sushan6/the-dev-board/assets/back-3d-pcb.PNG

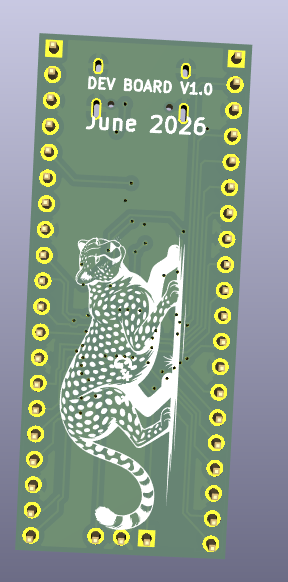
assets/back-3d-pcb.PNG
