sushan6/the-dev-board/assets/cart-1.PNG

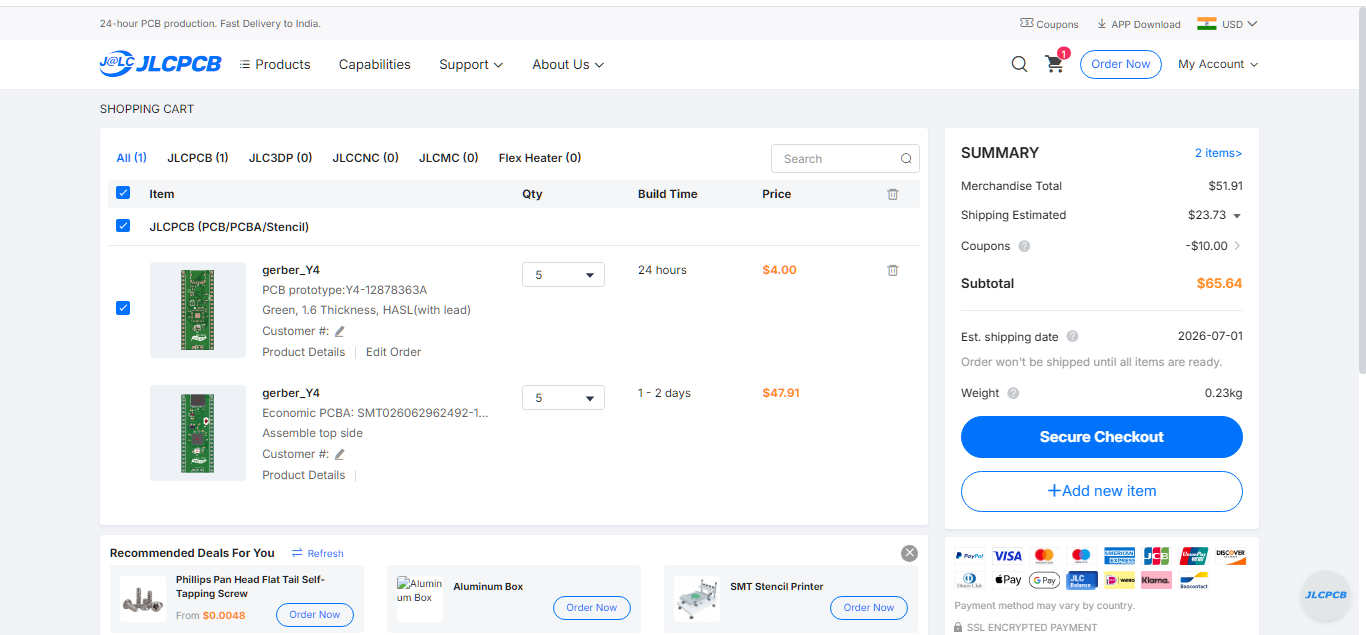
assets/cart-1.PNG
