sushan6/the-dev-board/assets/cart-2-1.PNG

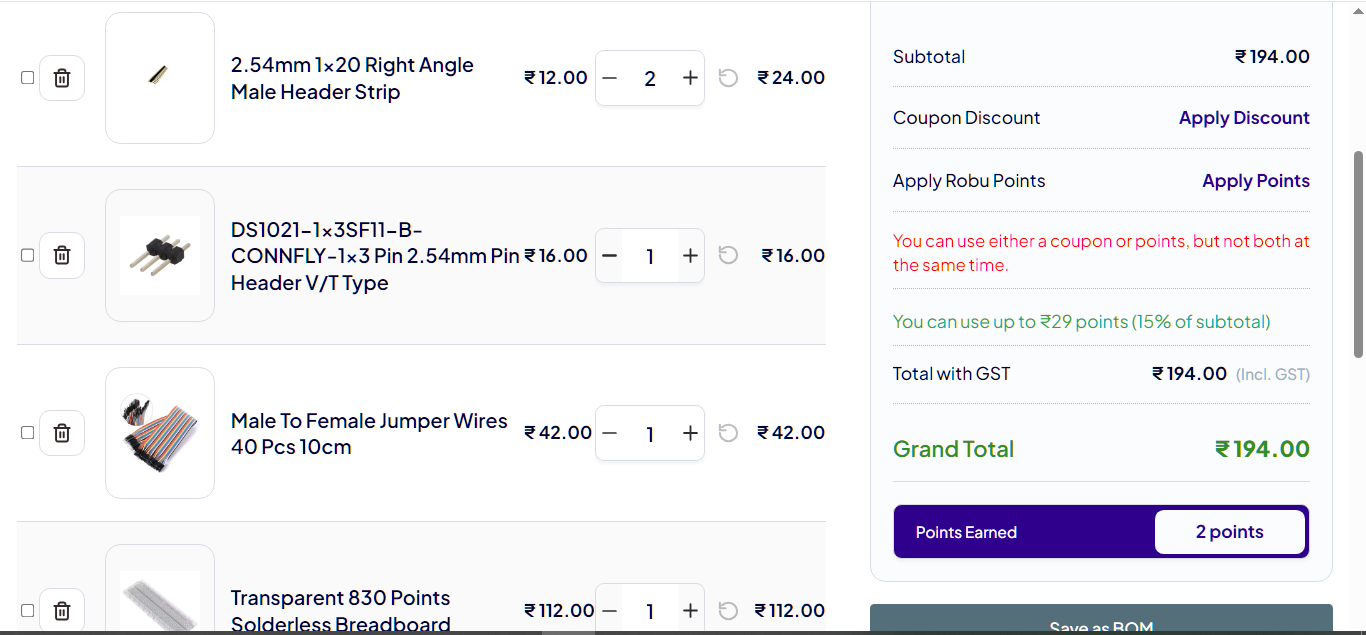
assets/cart-2-1.PNG
