sushan6/the-dev-board/assets/cart-2-2.PNG

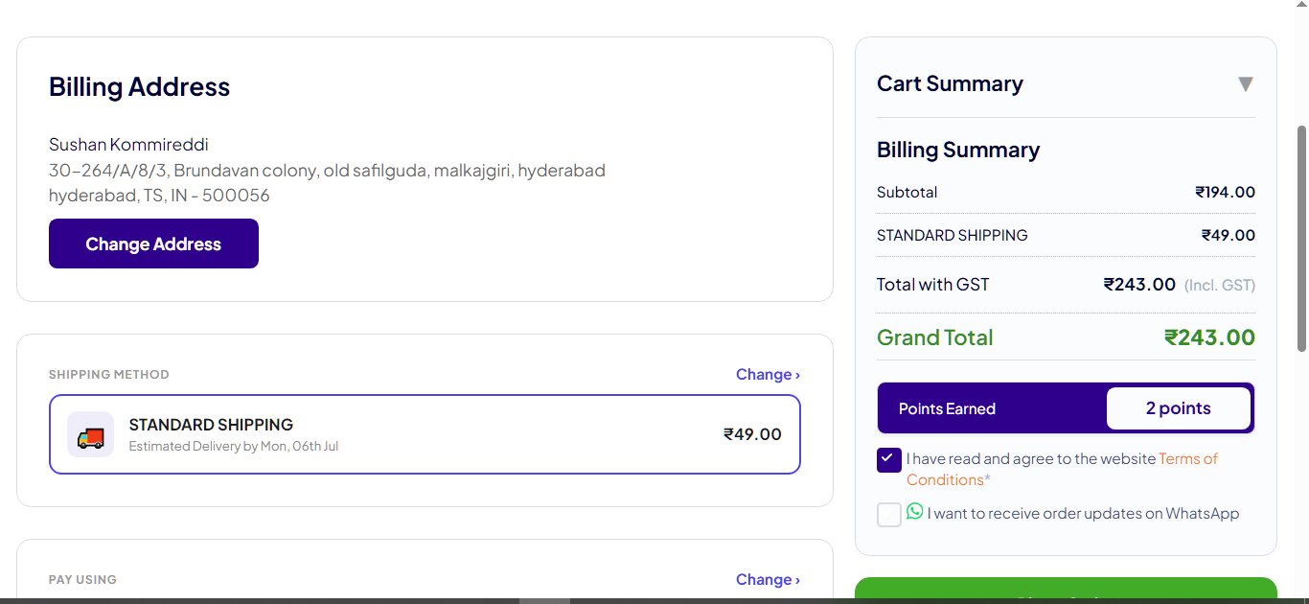
assets/cart-2-2.PNG
