sushan6/the-dev-board/assets/cart-digikey.PNG

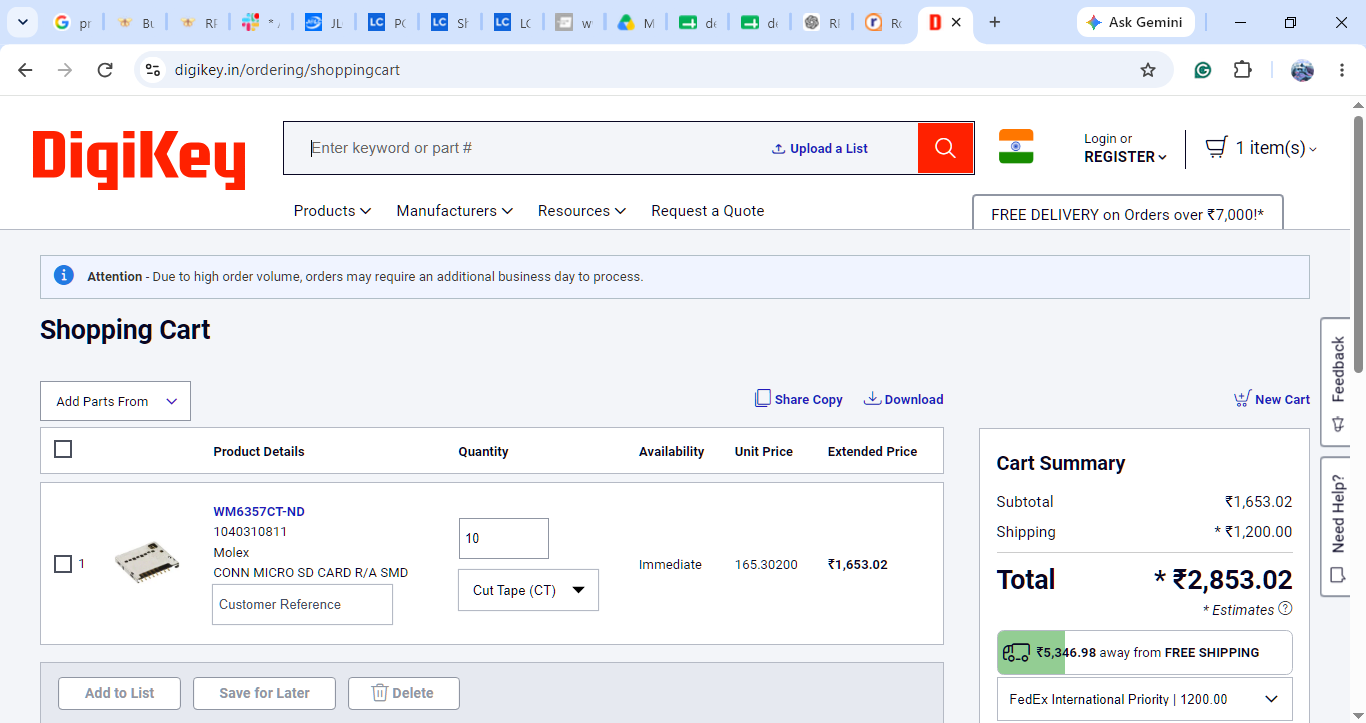
assets/cart-digikey.PNG
