sushan6/the-dev-board/assets/cart-robu.PNG

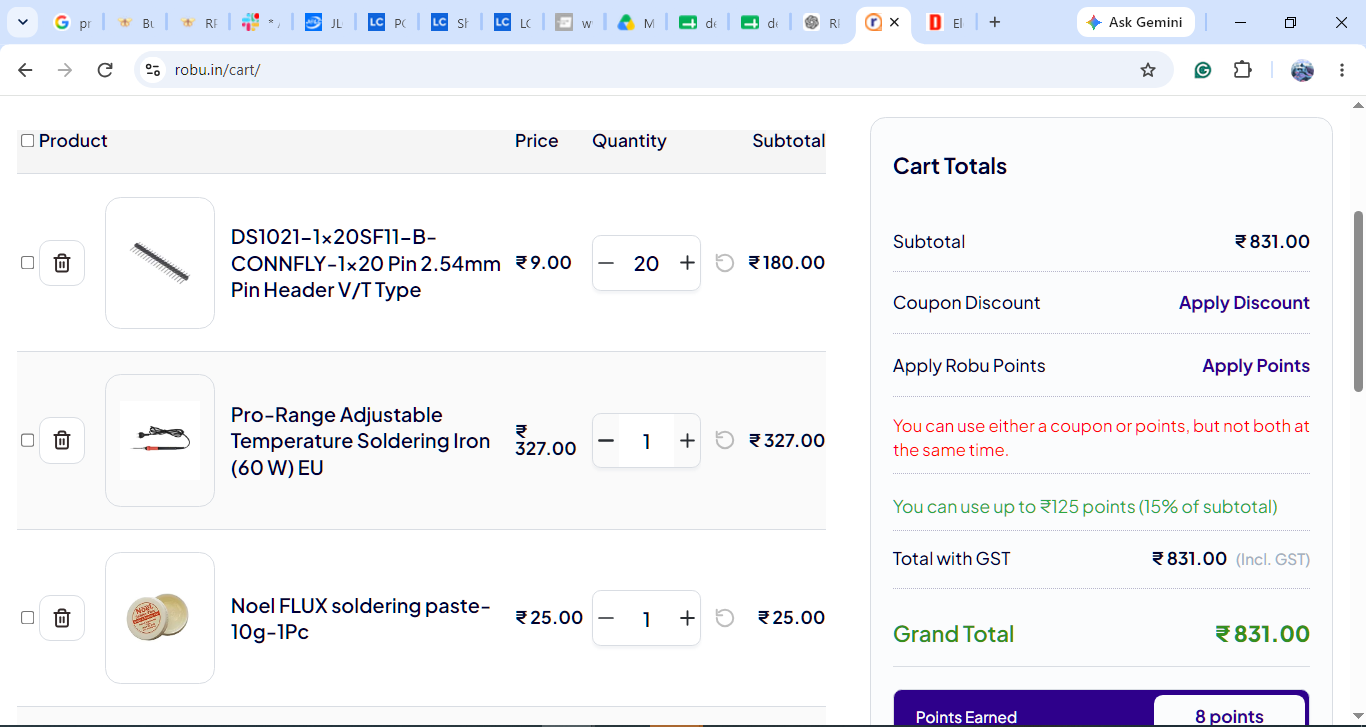
assets/cart-robu.PNG
