sushan6/the-dev-board/assets/cheetah.png

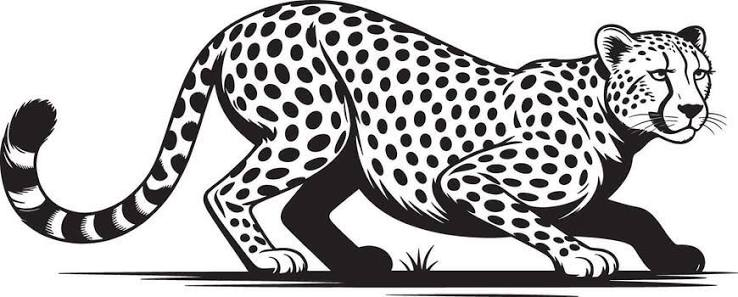
assets/cheetah.png
