sushan6/the-dev-board/assets/front-3d-pcb.PNG

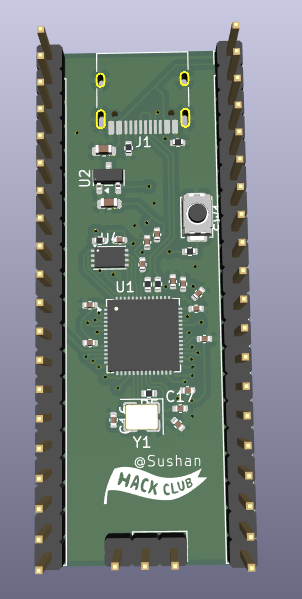
assets/front-3d-pcb.PNG
