sushan6/the-dev-board/assets/pcb image1.PNG

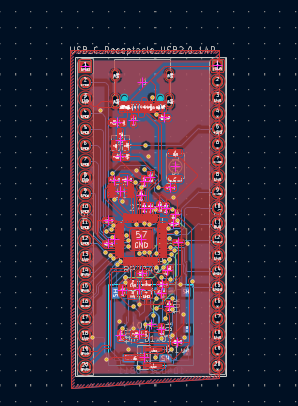
assets/pcb image1.PNG
